Brian1273/ECE_411/Project_Metronome/Images/1bba2a5ce60771511d11608d5c51a1ac.png

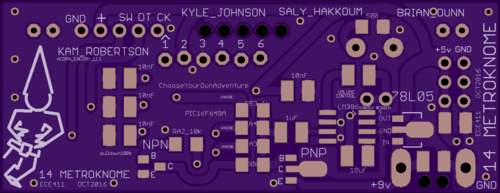
Project_Metronome/Images/1bba2a5ce60771511d11608d5c51a1ac.png
