Brian1273/ECE_411/Project_Metronome/Images/6ba66605eb475a37e0fe1be445c7c349.png

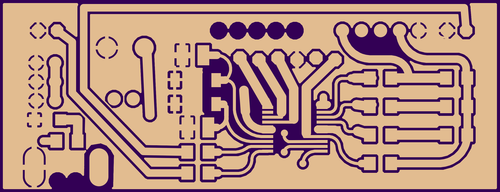
Project_Metronome/Images/6ba66605eb475a37e0fe1be445c7c349.png
