Brian1273/ECE_411/Project_Metronome/Images/8fa9e825b72547140c963421e77560f3.png

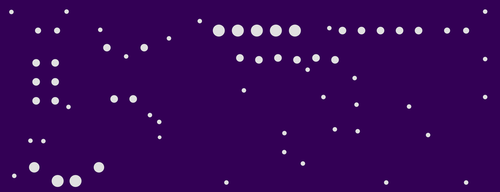
Project_Metronome/Images/8fa9e825b72547140c963421e77560f3.png
