Brian1273/ECE_411/Project_Metronome/Images/9c15492ab461137f4646b0bf2be28633.png

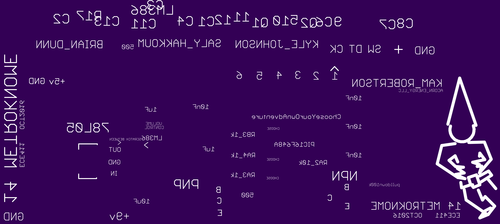
Project_Metronome/Images/9c15492ab461137f4646b0bf2be28633.png
