Brian1273/ECE_411/Project_Metronome/Images/101_9720.JPG

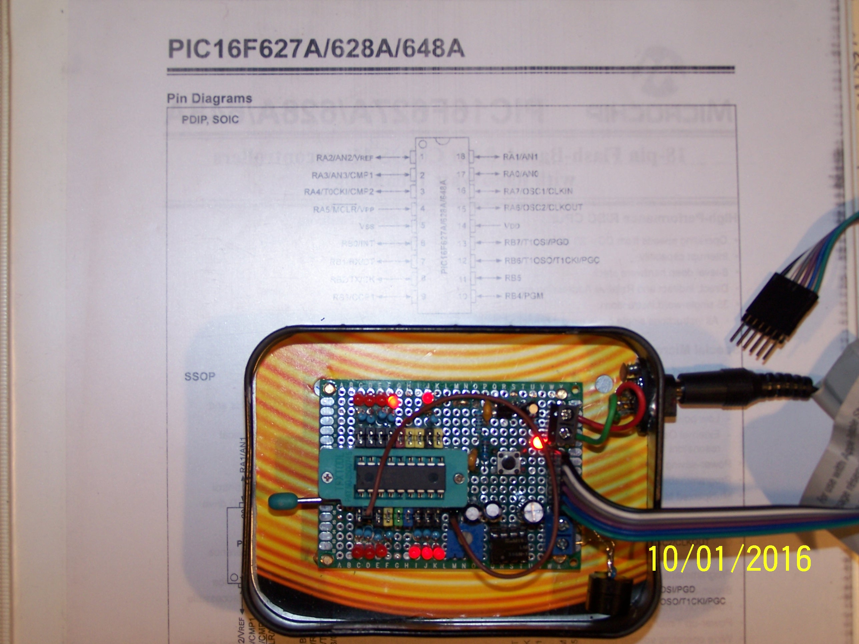
Project_Metronome/Images/101_9720.JPG
