Brian1273/ECE_411/Project_Metronome/Images/988fbb8f686a4b56be6c816c8a2c592c.png

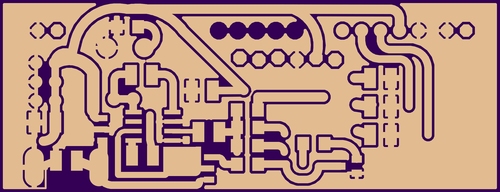
Project_Metronome/Images/988fbb8f686a4b56be6c816c8a2c592c.png
