Brian1273/ECE_411/Project_Metronome/Images/8753ae672788ae1bc2547449676f1f89.png

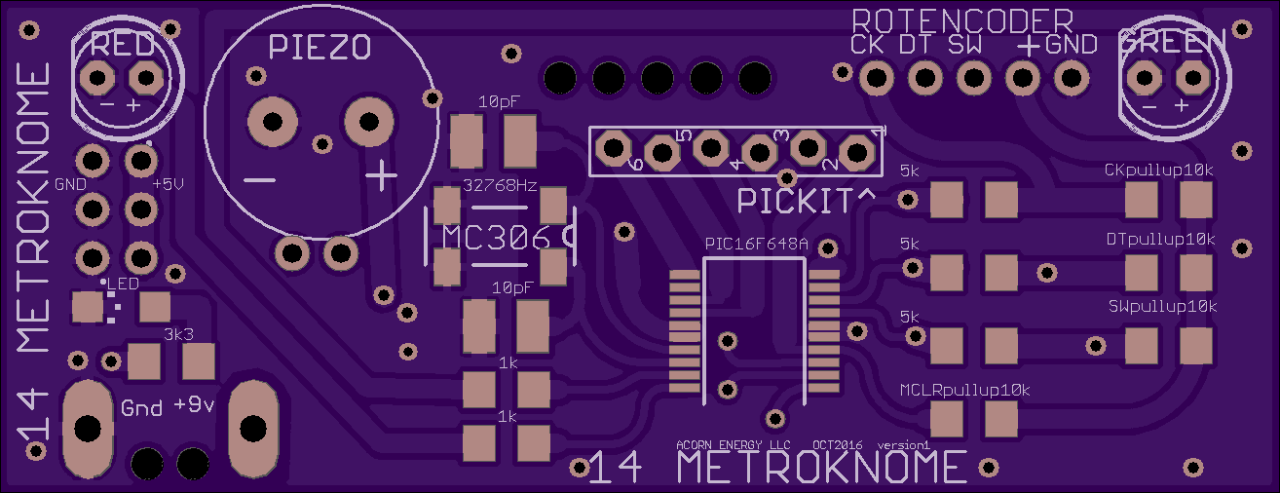
Project_Metronome/Images/8753ae672788ae1bc2547449676f1f89.png
