Brian1273/ECE_411/Project_Metronome/Images/58837b1c782eb02489fb9ee66505fd8d.png

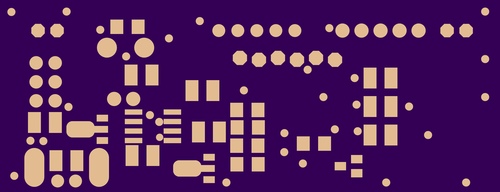
Project_Metronome/Images/58837b1c782eb02489fb9ee66505fd8d.png
