Brian1273/ECE_411/Project_Metronome/Images/b5737353886c539f5db4e616d0e1083c.png

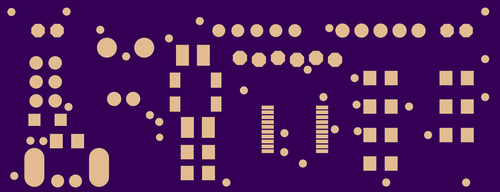
Project_Metronome/Images/b5737353886c539f5db4e616d0e1083c.png
