Brian1273/ECE_411/Project_Metronome/Images/Board_rev_01.PNG

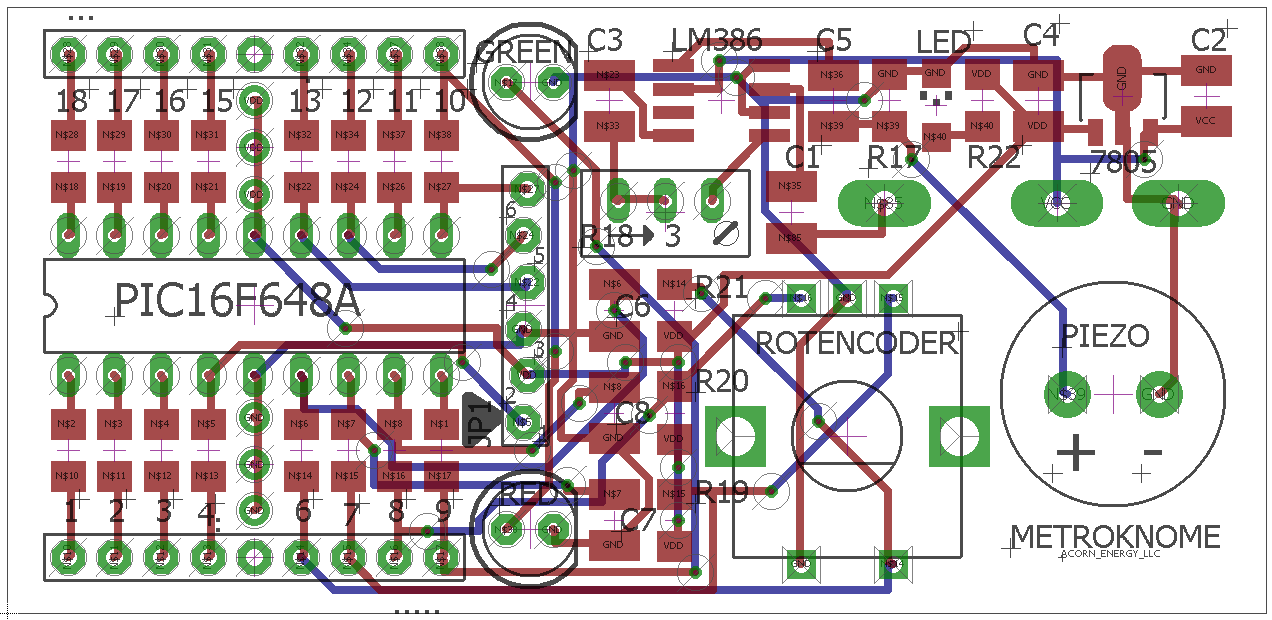
Project_Metronome/Images/Board_rev_01.PNG
