Brian1273/ECE_411/Project_Metronome/Images/d55b43c2cb4ecbdca08913ed9a557aac.png

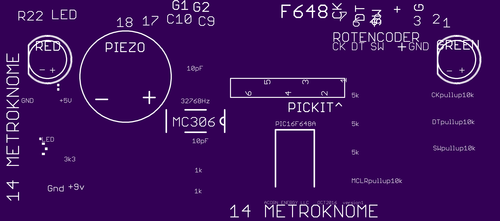
Project_Metronome/Images/d55b43c2cb4ecbdca08913ed9a557aac.png
