Brian1273/ECE_411/Project_Metronome/Images/Program Flow Chart.png

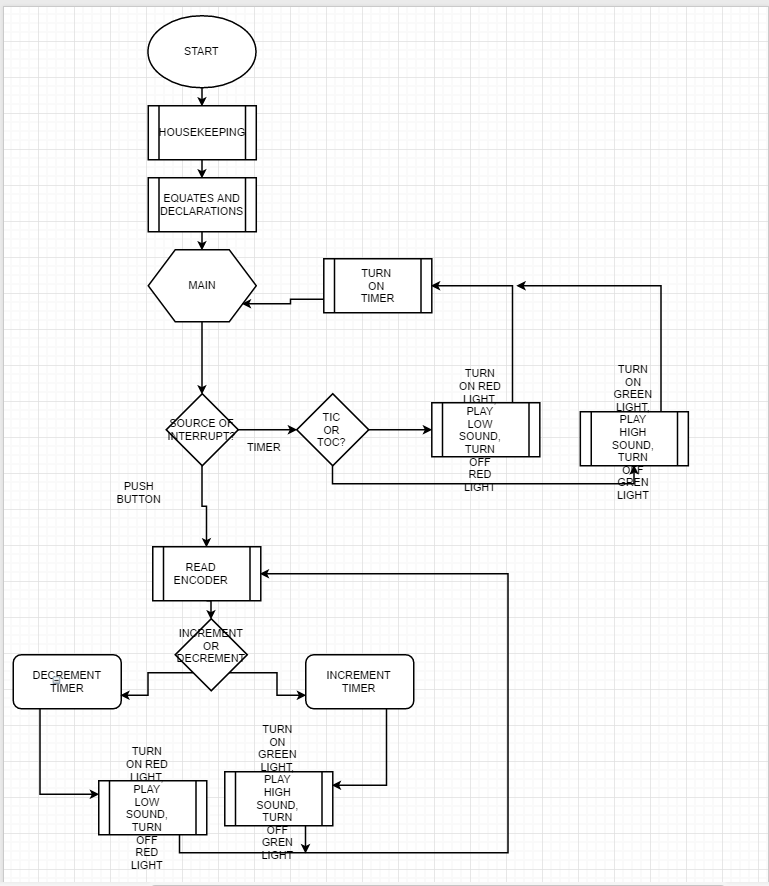
Project_Metronome/Images/Program Flow Chart.png
