Brian1273/ECE_411/Project_Metronome/Images/Progress_Images/pre-final_sol.jpg

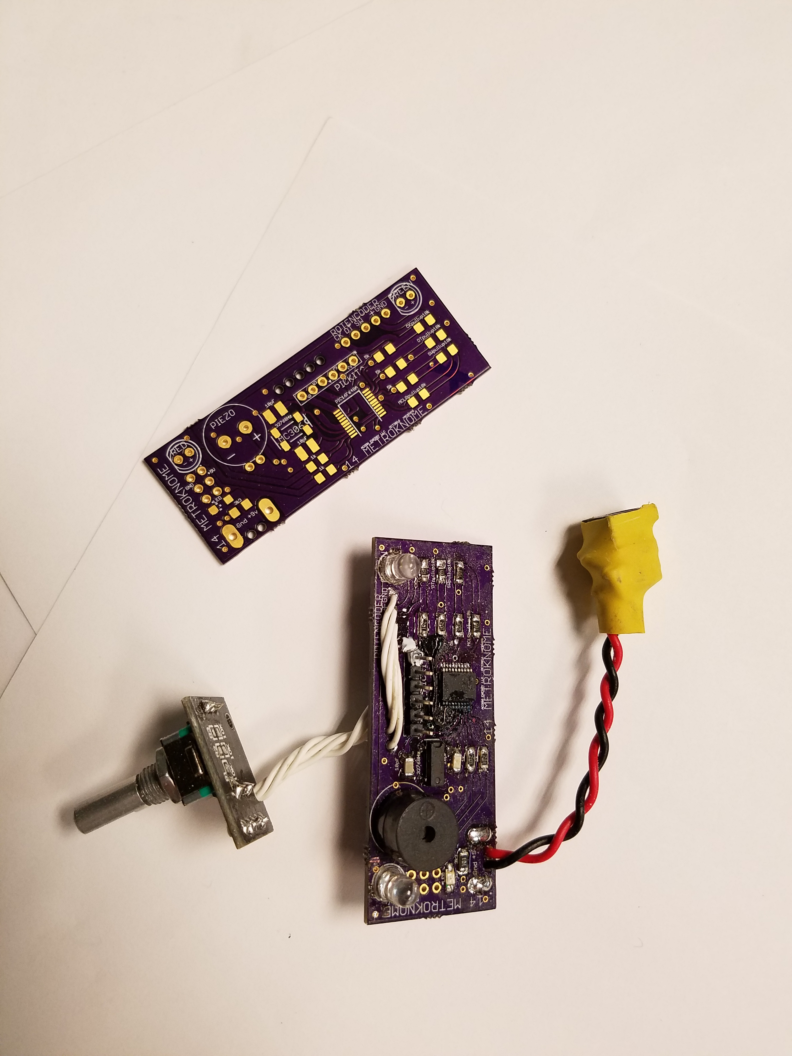
Project_Metronome/Images/Progress_Images/pre-final_sol.jpg
