Brian1273/ECE_411/Project_Metronome/Images/Progress_Images/proto_02.jpg

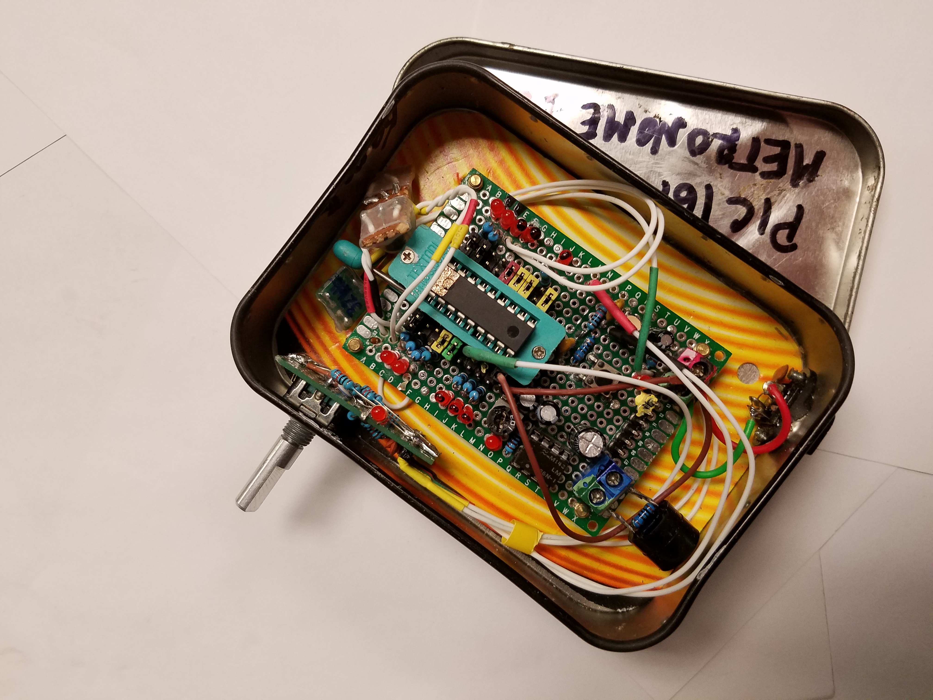
Project_Metronome/Images/Progress_Images/proto_02.jpg
