Brian1273/ECE_411/Project_Metronome/Images/Progress_Images/tools_01.jpg

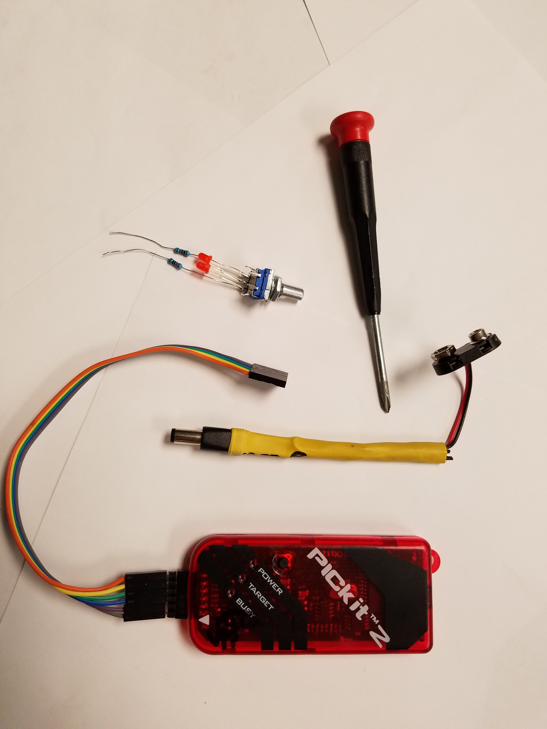
Project_Metronome/Images/Progress_Images/tools_01.jpg
