Brian1273/ECE_411/Project_Metronome/METROKNOME.png

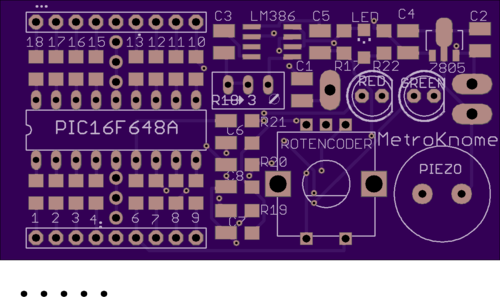
Project_Metronome/METROKNOME.png
