Brian1273/ECE_411/Project_Metronome/METROKNOME_BAK.png

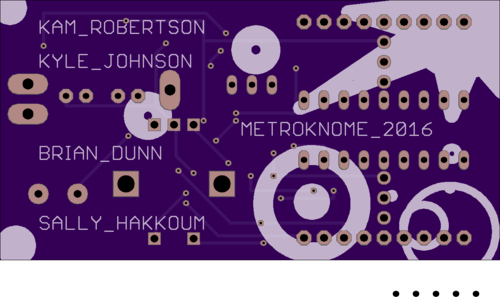
Project_Metronome/METROKNOME_BAK.png
