Brian1273/ECE_411/Project_Metronome/Schematics/48ab9222b0aee31de85262ba45df444d.png

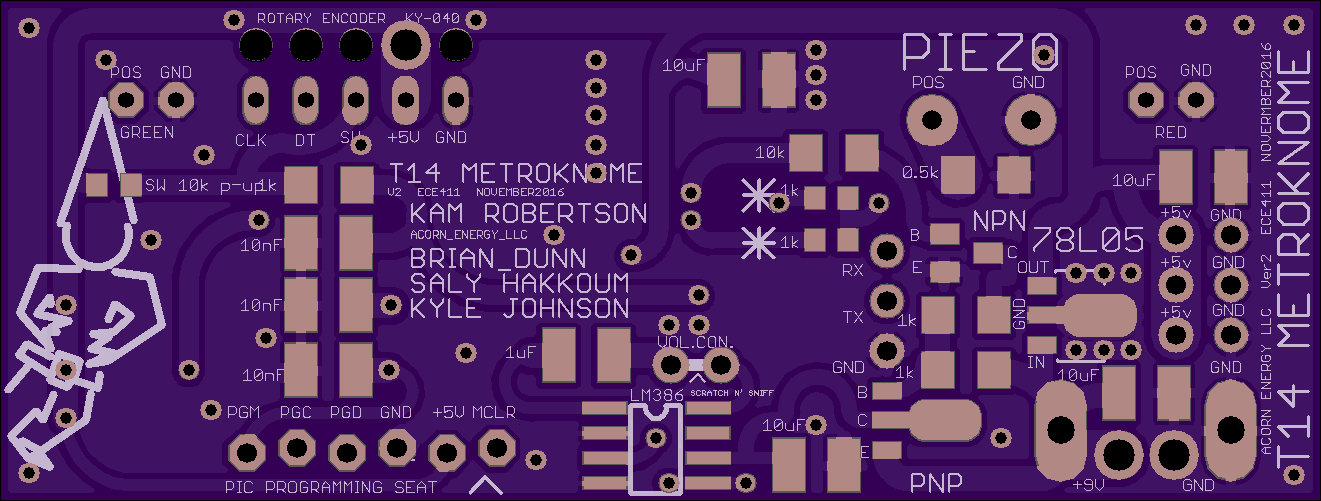
Project_Metronome/Schematics/48ab9222b0aee31de85262ba45df444d.png
