Brian1273/ECE_411/Project_Metronome/Schematics/632eb32480f59fcbdeea132bf39b1ebc.png

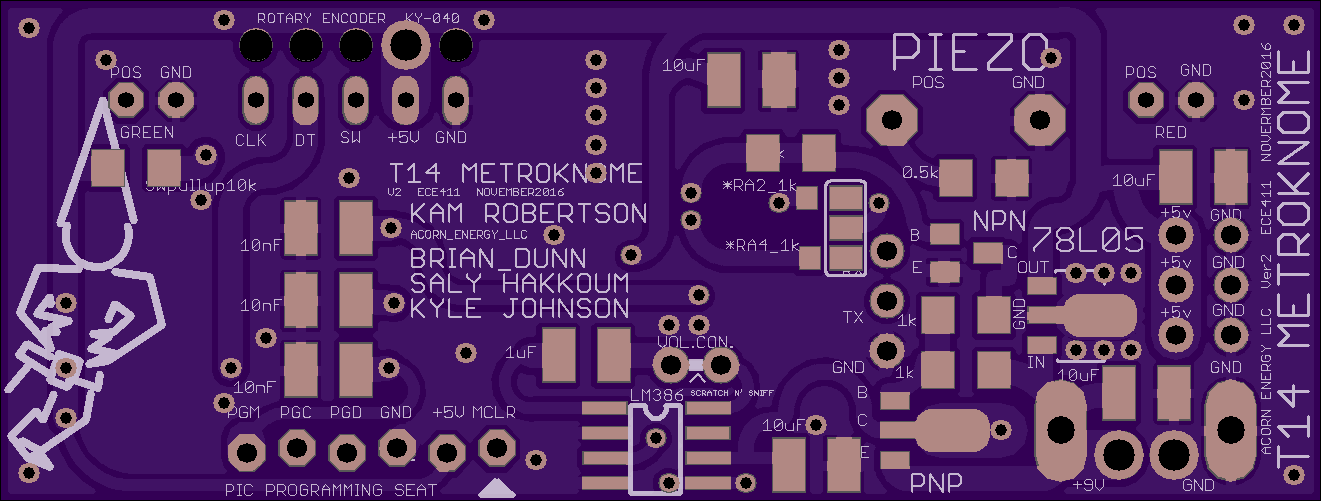
Project_Metronome/Schematics/632eb32480f59fcbdeea132bf39b1ebc.png
