Brian1273/ECE_411/Project_Metronome/Schematics/layout_image.PNG

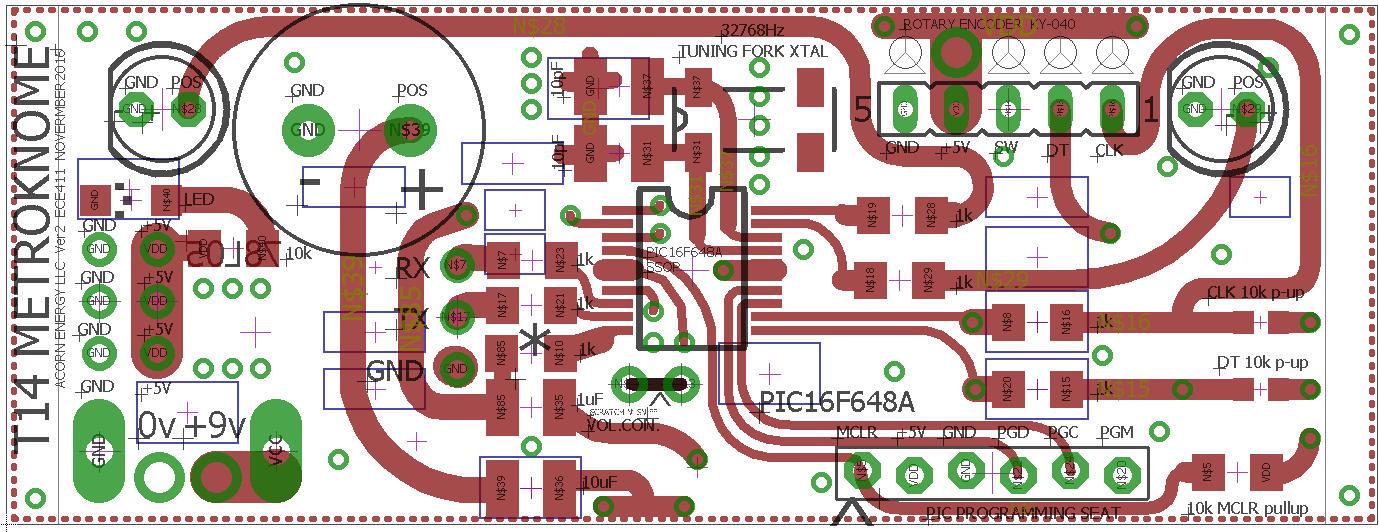
Project_Metronome/Schematics/layout_image.PNG
