Brian1273/ECE_411/Project_Metronome/Schematics/MetroKnome Schematic.png

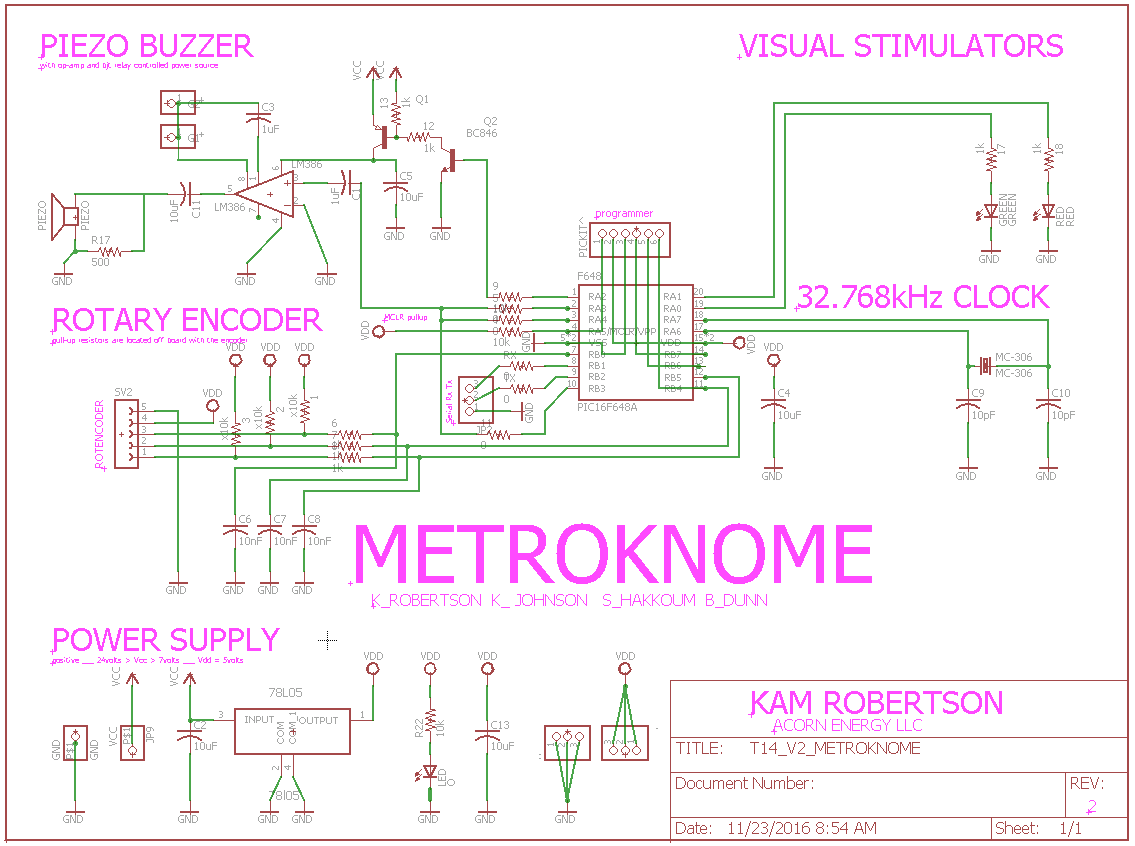
Project_Metronome/Schematics/MetroKnome Schematic.png
