Brian1273/ECE_411/Project_Metronome/Schematics/DevBoard.asc

BUTTON: csw
C1: cap; 10µ
C2: cap; 220µ
C3: cap; 10µ
C4: cap
C5: cap; 10n
C6: cap; 330n
D1: LED
D2: LED
D3: LED
D4: LED
D5: LED
D6: LED
D7: LED
D8: LED
D9: LED
D10: LED
D11: LED
LM78L05: LT1587
LM386: DIP8
PIC16F648A: DIP20
R1: res; 100
R2: res; 1k
R3: res; 1k
R4: res; 1k
R5: res; 1k
R6: res; 1k
R7: res; 1k
R8: res; 1k
R9: res; 1k
R10: res; 1k
R11: res; 1k
R12: res; 0
R13: res; 1k
R14: res; 10K
R15: res; 10k
R16: res; 10k
V2: battery; 9
VOLUME: res; 10K
Named nets: 0, nc, 9v, audio_output, audio_input, 5.1v, PDG, PGC, MCLR, pickit3, 5.1V, opamp
needs sorting
needs sorting
and should
be closer to
int pin
KAM ROBERTSON
ECE411 DEV. BOARD
OCTOBER 2016
RESET BUTTON 
TO GROUND
GOES HERE
likely solution 
for volume
